Wedenborg/FermentationBox/photos/20220815_230204.jpg

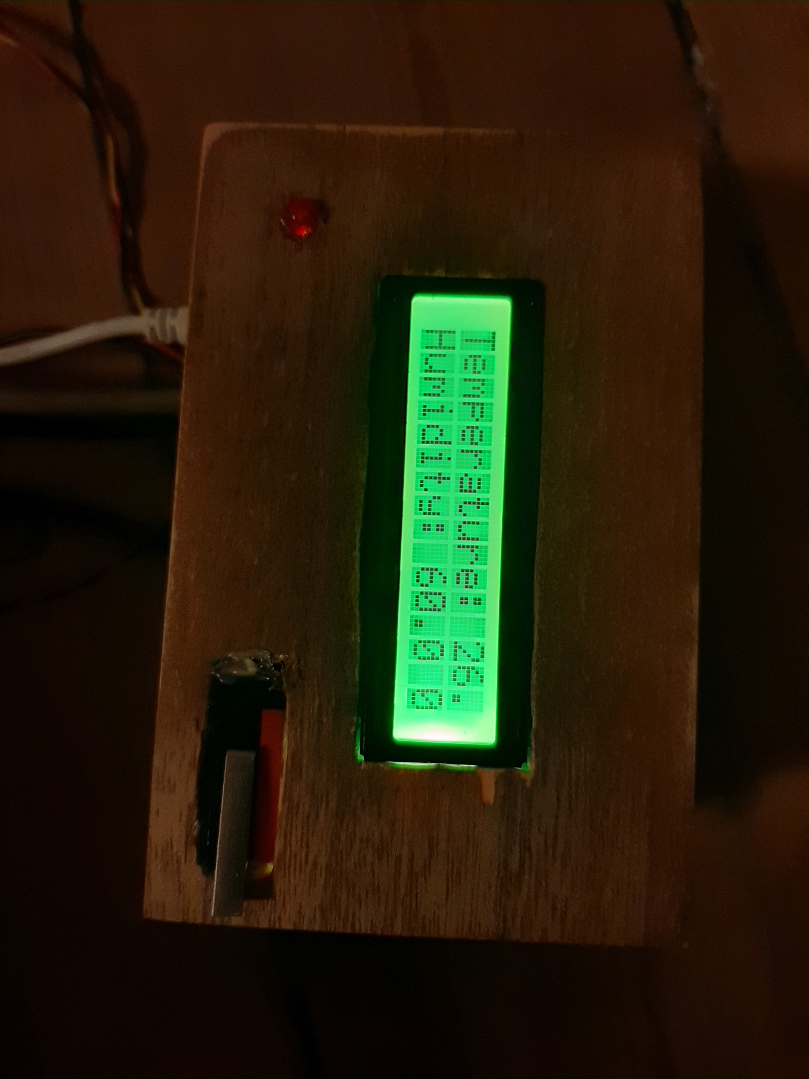
photos/20220815_230204.jpg
