Wedenborg/FermentationBox/photos/20220815_225837.jpg

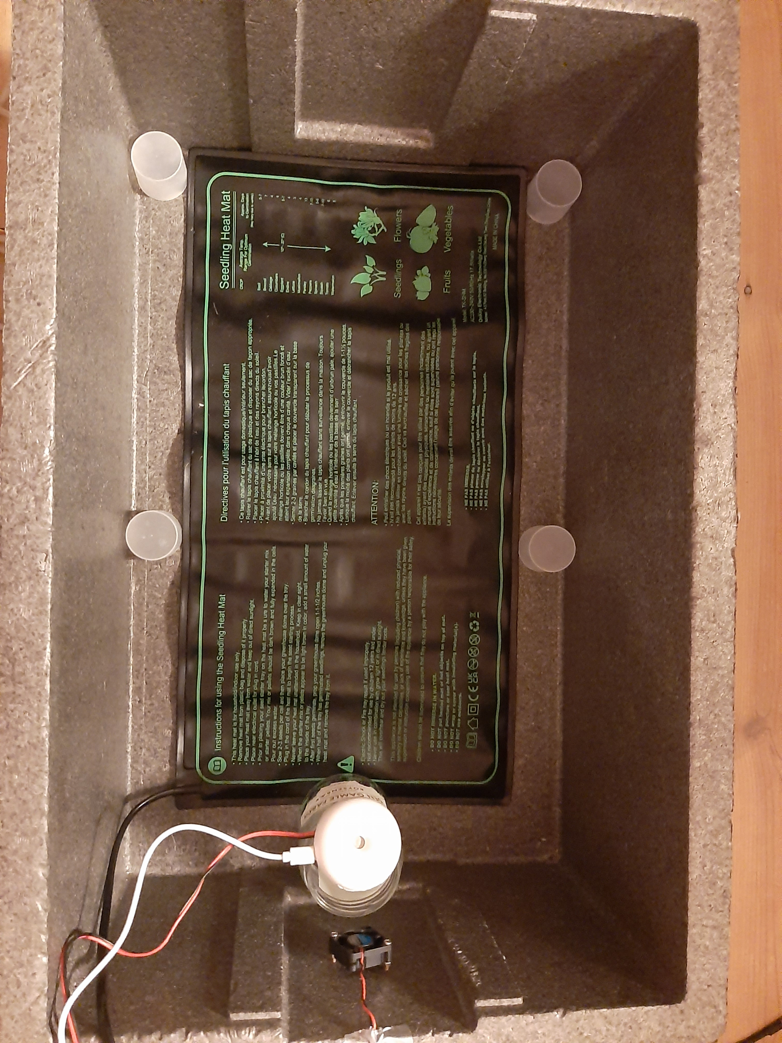
photos/20220815_225837.jpg
